asteinig4018/double_wheel/wheel_rollers.SLDPRT

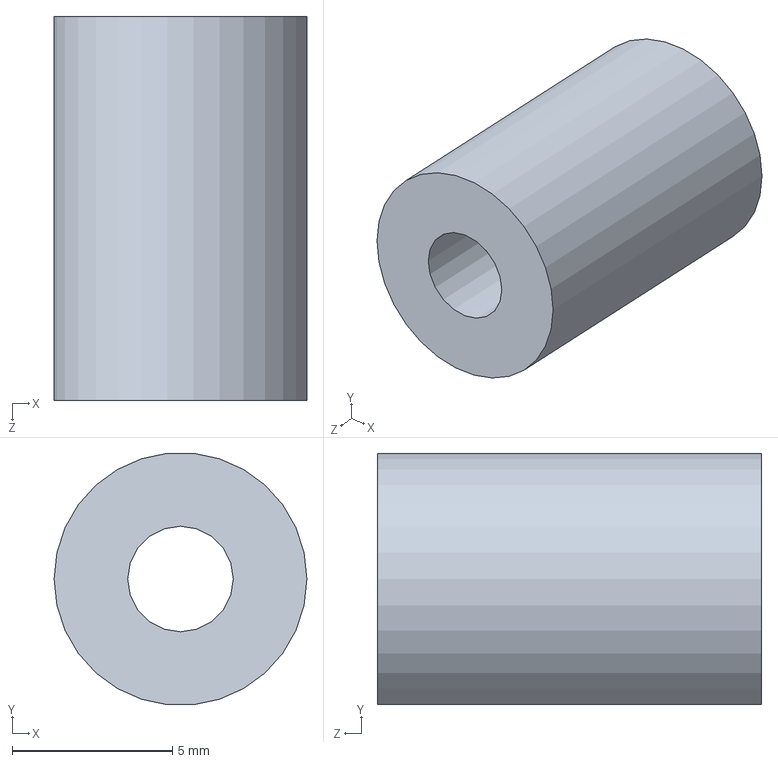
[picture p16: CAD file, 2020-08-16]
wheel_rollers.SLDPRT
7.90 x 7.86 x 12.0 mm
