asteinig4018/double_wheel/wheel_v1.SLDPRT

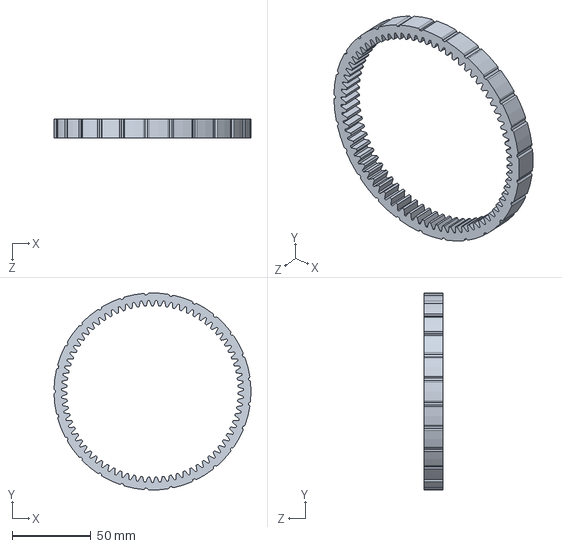
[picture p17: CAD file, 2020-08-12]
wheel_v1.SLDPRT
125.0 x 124.9 x 12.0 mm
