asteinig4018/double_wheel/stls/wheel_axle_v6.STL

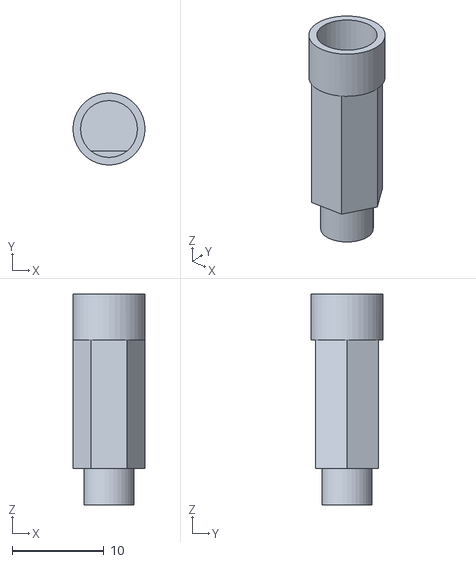
[picture p18: CAD file, 2020-08-15]
stls/wheel_axle_v6.STL
7.90 x 7.85 x 23.0
