asteinig4018/double_wheel/Kohree_motor.SLDPRT

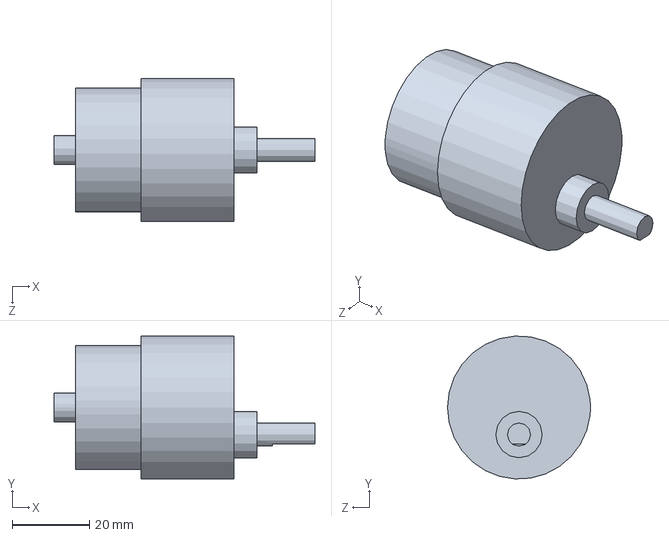
[picture p19: CAD file, 2020-08-12]
Kohree_motor.SLDPRT
67.5 x 36.9 x 37.0 mm
