asteinig4018/double_wheel/roller_pin.SLDPRT

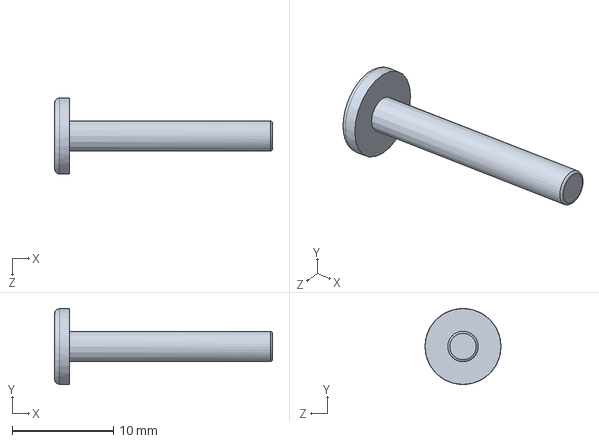
[picture p20: CAD file, 2020-08-08]
roller_pin.SLDPRT
21.5 x 7.50 x 7.50 mm
