asteinig4018/double_wheel/stls/axle_inner_tester.STL

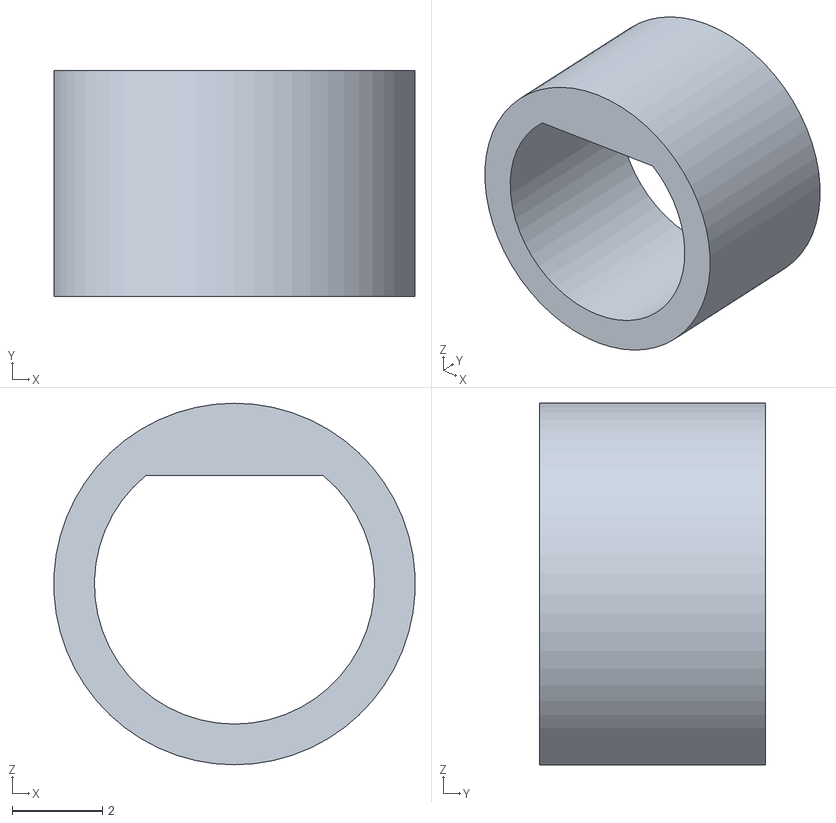
[picture p21: CAD file, 2020-08-15]
stls/axle_inner_tester.STL
7.99 x 5.00 x 8.00
