asteinig4018/double_wheel/stls/axle_tester.STL

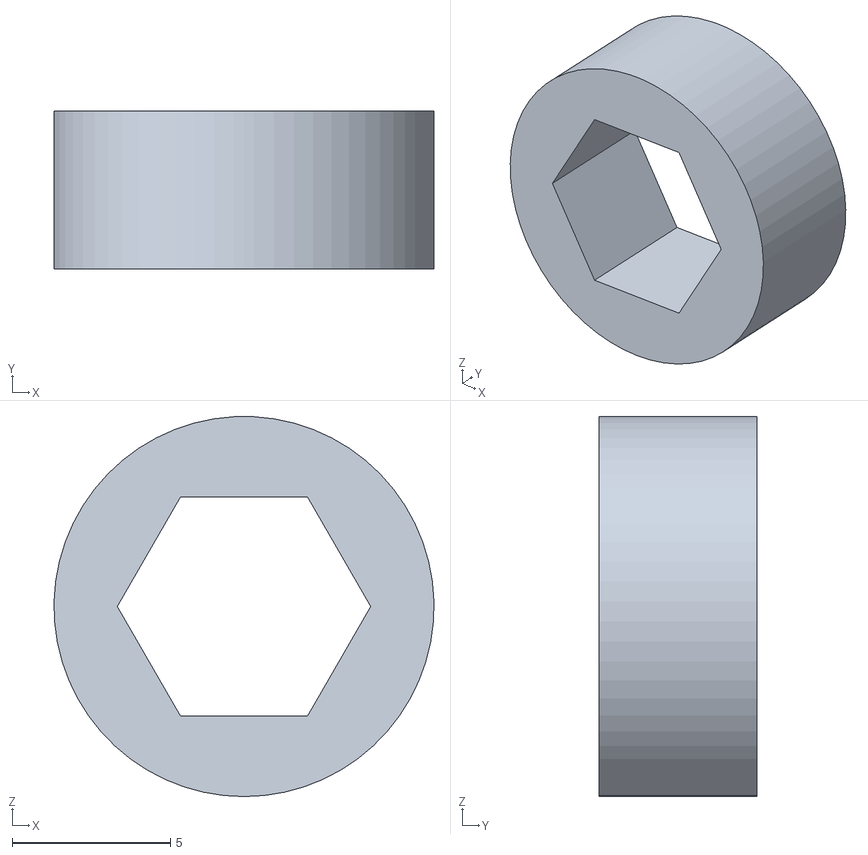
[picture p22: CAD file, 2020-08-13]
stls/axle_tester.STL
12.0 x 5.00 x 12.0
