asteinig4018/double_wheel/stls/roller_pin_v1.STL

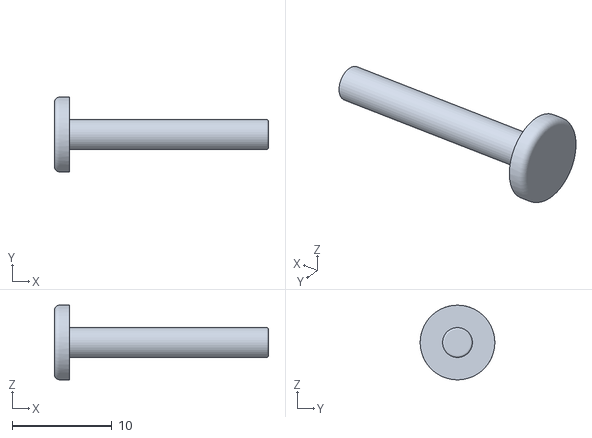
[picture p23: CAD file, 2020-08-08]
stls/roller_pin_v1.STL
21.5 x 7.50 x 7.50
